Rhamao/DemoNixie/DemoNixie-KiCad/images/Screenshot from 2020-06-03 17-16-17.png

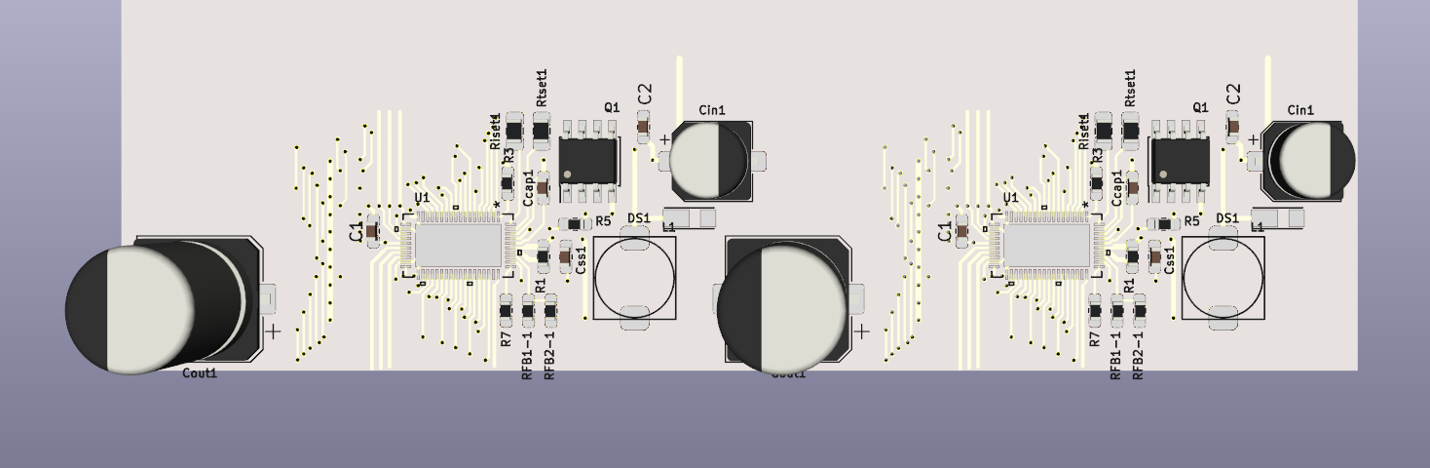
DemoNixie-KiCad/images/Screenshot from 2020-06-03 17-16-17.png
