Rhamao/DemoNixie/DemoNixieControl-KiCad/images/masseBOTTOM.png

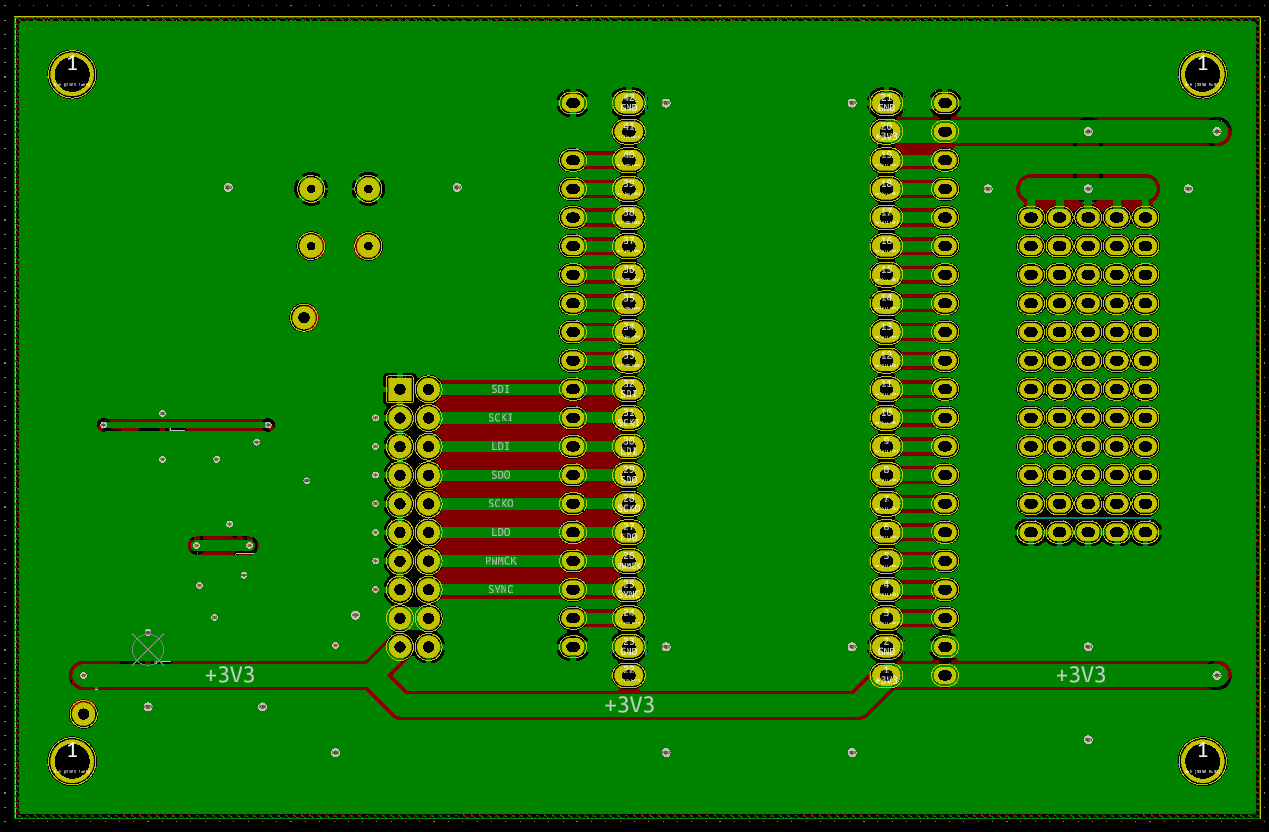
DemoNixieControl-KiCad/images/masseBOTTOM.png
