Rhamao/DemoNixie/DemoNixieControl-KiCad/images/routage.png

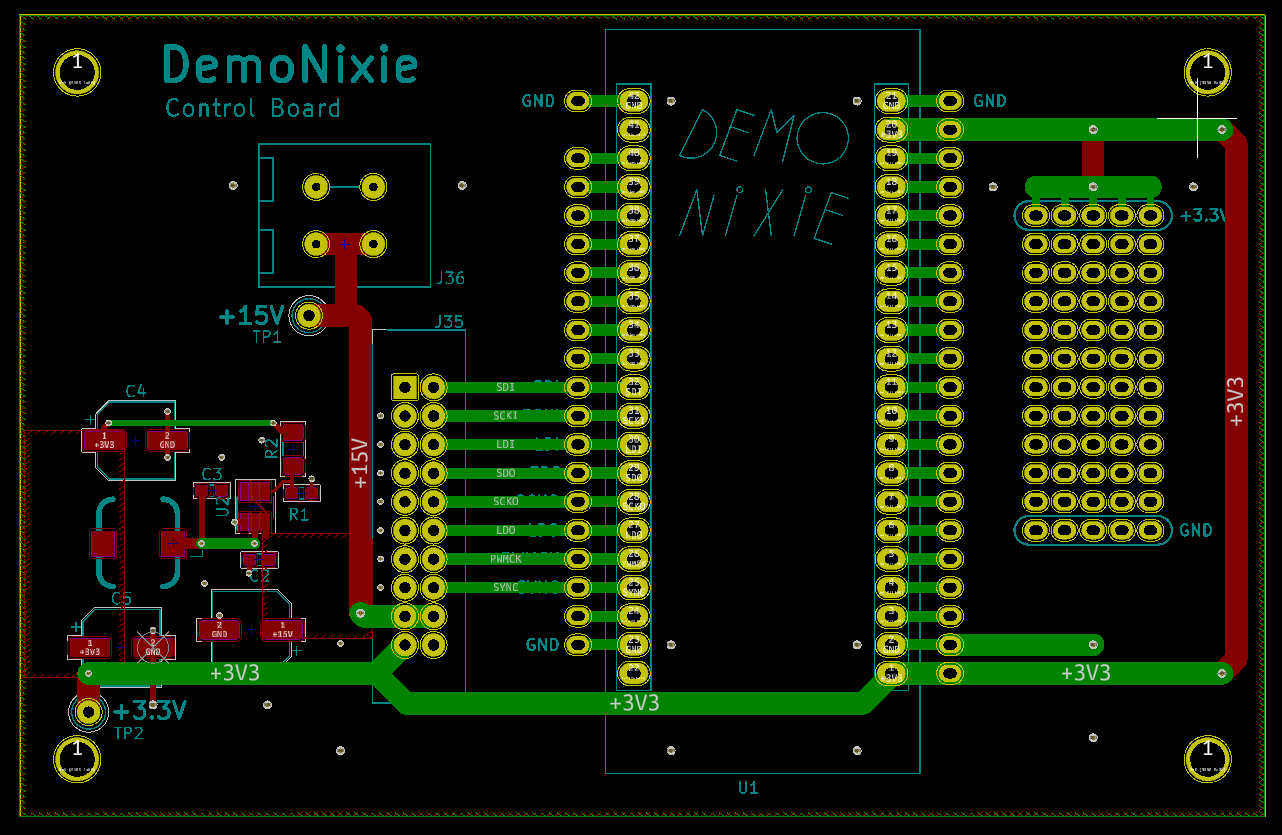
DemoNixieControl-KiCad/images/routage.png
